tobychui/DIY-60W-PD-Powerbank/Photo/273100965_10218137502903919_1505471354527480093_n.jpg

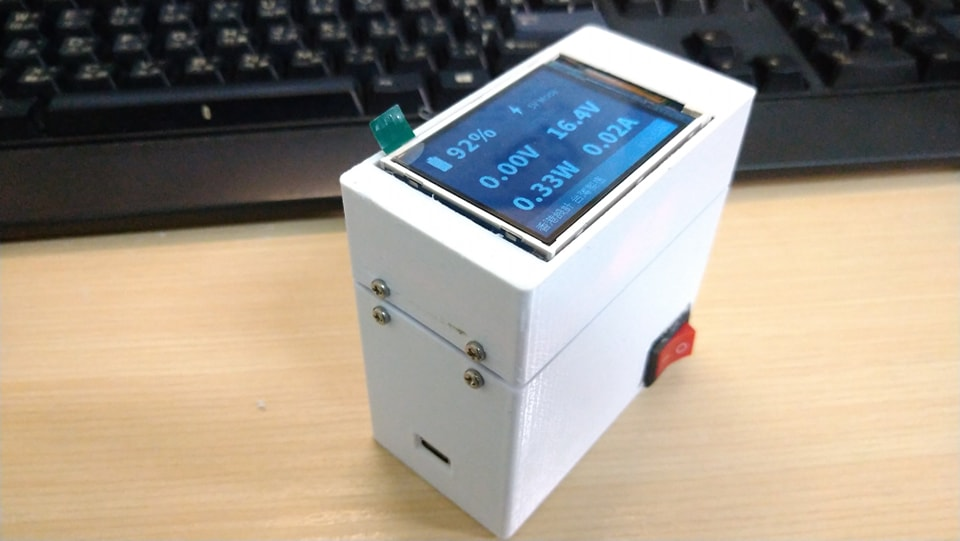
Photo/273100965_10218137502903919_1505471354527480093_n.jpg
