tobychui/DIY-60W-PD-Powerbank/Photo/DSC_0626.JPG

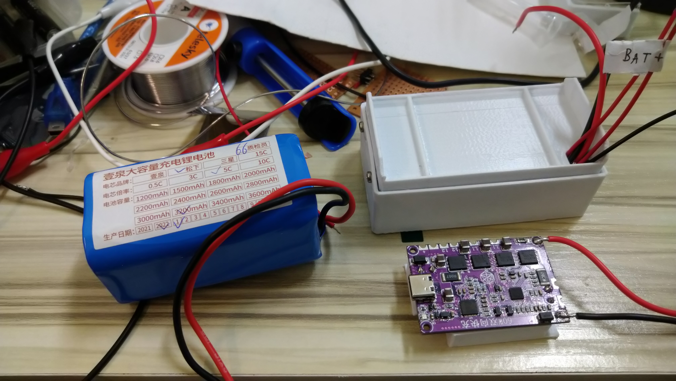
Photo/DSC_0626.JPG
