tobychui/DIY-60W-PD-Powerbank/Photo/DSC_0627.JPG

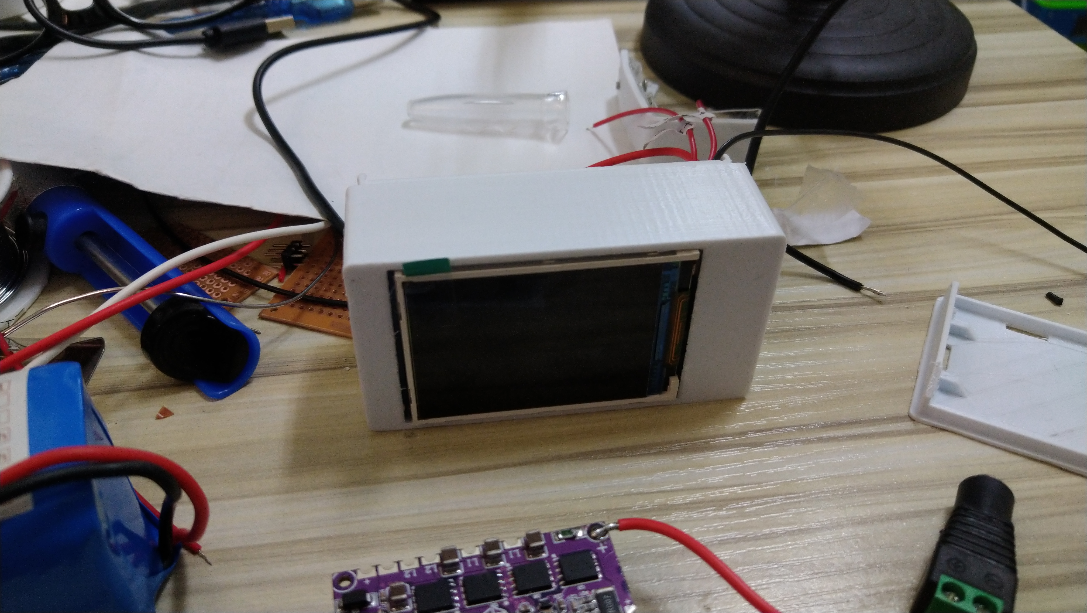
Photo/DSC_0627.JPG
