tobychui/DIY-60W-PD-Powerbank/Photo/DSC_0629.JPG

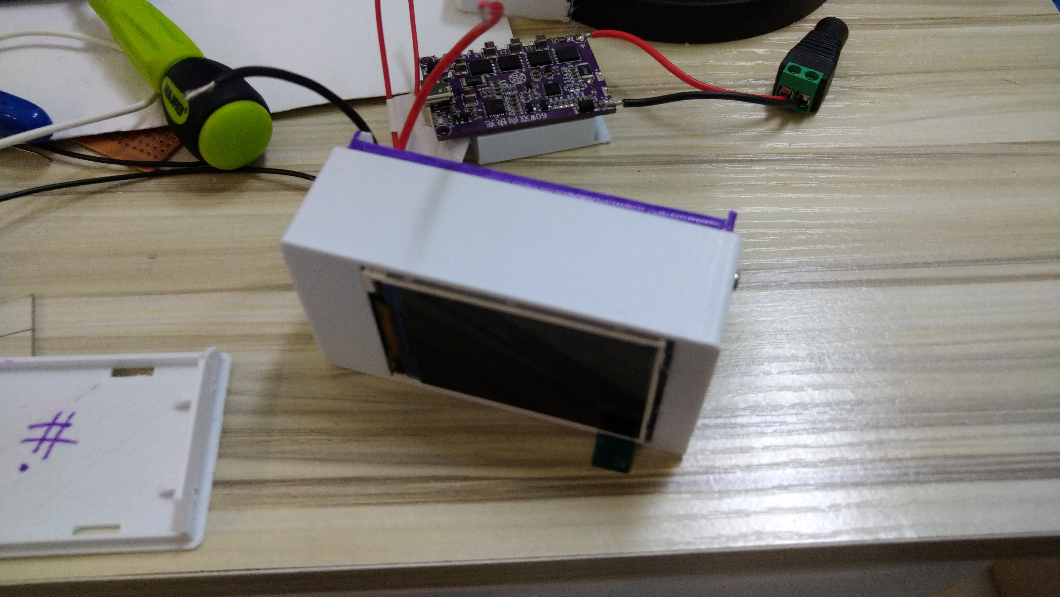
Photo/DSC_0629.JPG
