tobychui/DIY-60W-PD-Powerbank/Photo/DSC_0630.JPG

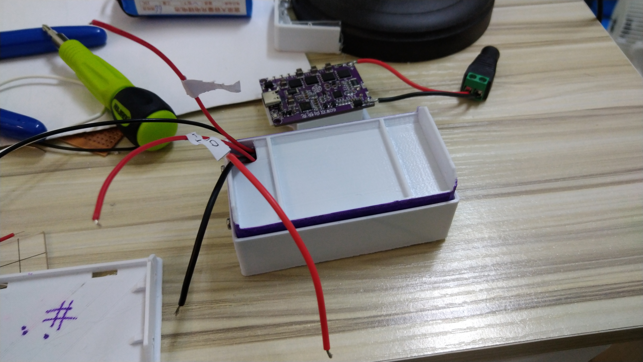
Photo/DSC_0630.JPG
