tobychui/DIY-60W-PD-Powerbank/Photo/DSC_0631.JPG

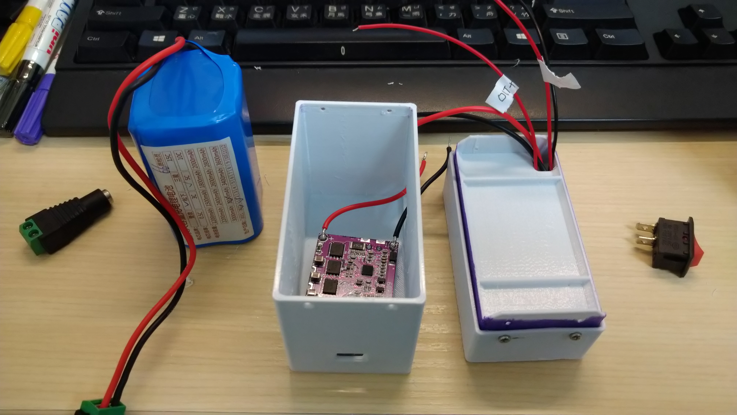
Photo/DSC_0631.JPG
