tobychui/DIY-60W-PD-Powerbank/Photo/DSC_0632.JPG

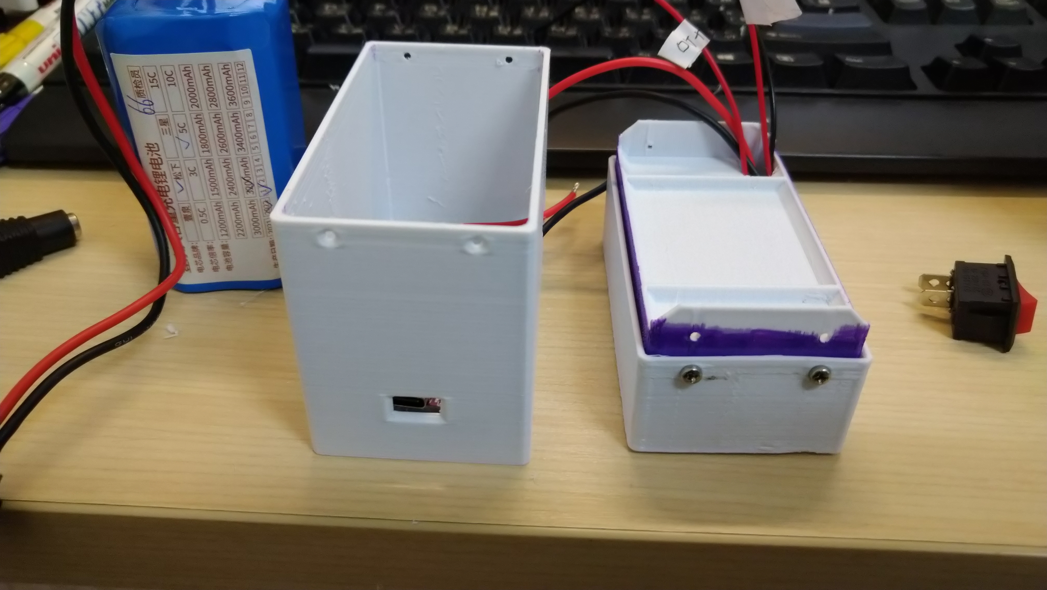
Photo/DSC_0632.JPG
