tobychui/DIY-60W-PD-Powerbank/Photo/IMG_20220121_200404.jpg

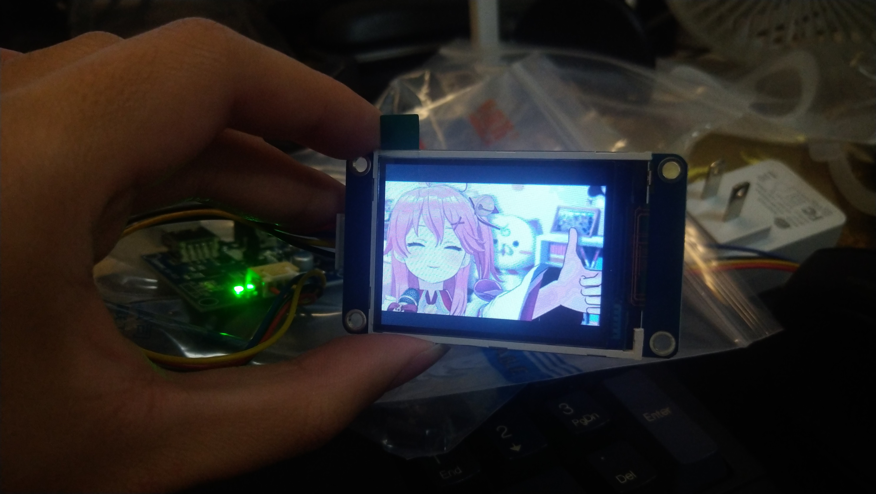
Photo/IMG_20220121_200404.jpg
