tobychui/DIY-60W-PD-Powerbank/Photo/IMG_20220121_230231.jpg

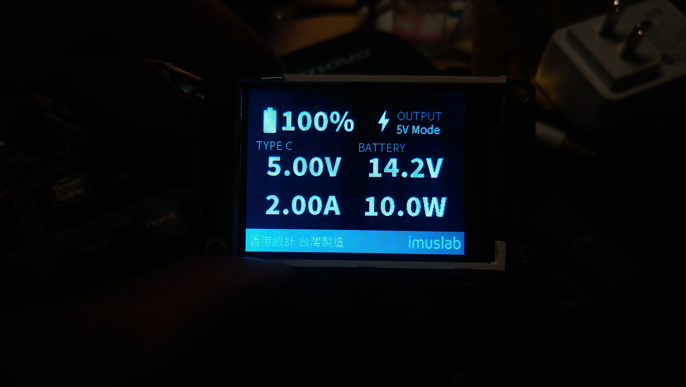
Photo/IMG_20220121_230231.jpg
