tobychui/DIY-60W-PD-Powerbank/Photo/IMG_20220121_230241.jpg

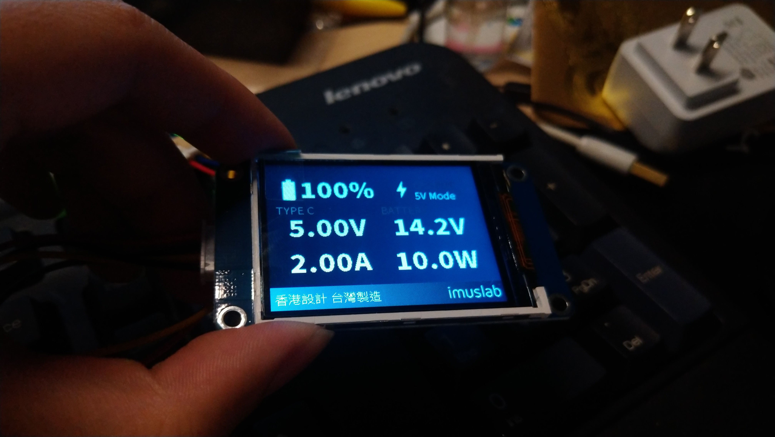
Photo/IMG_20220121_230241.jpg
