tobychui/DIY-60W-PD-Powerbank/Photo/IMG_20220125_193211.jpg

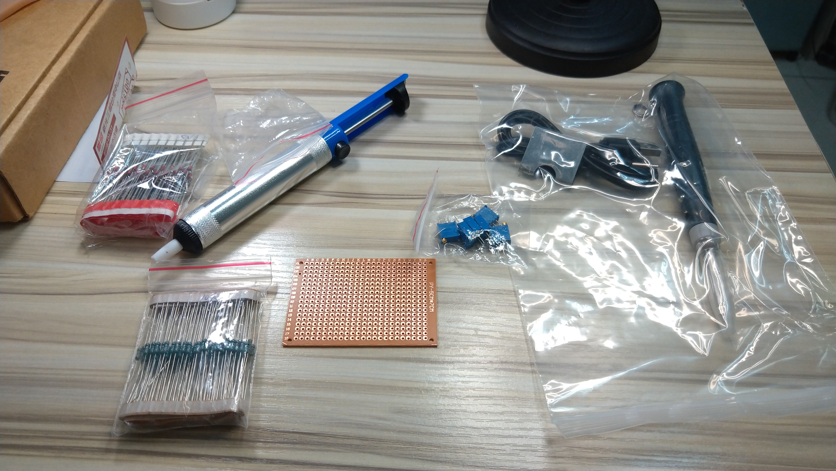
Photo/IMG_20220125_193211.jpg
