tobychui/DIY-60W-PD-Powerbank/Photo/IMG_20220125_210157.jpg

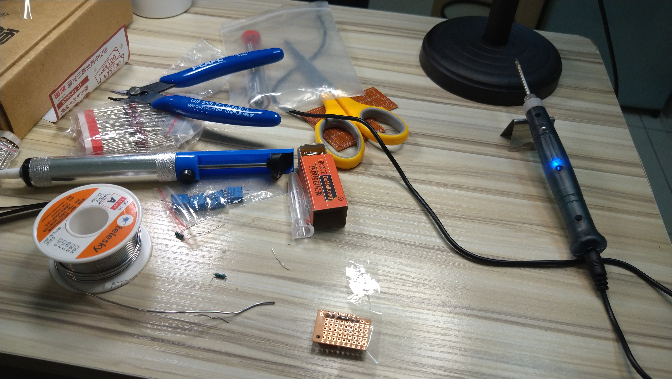
Photo/IMG_20220125_210157.jpg
