tobychui/DIY-60W-PD-Powerbank/Photo/IMG_20220125_210558.jpg

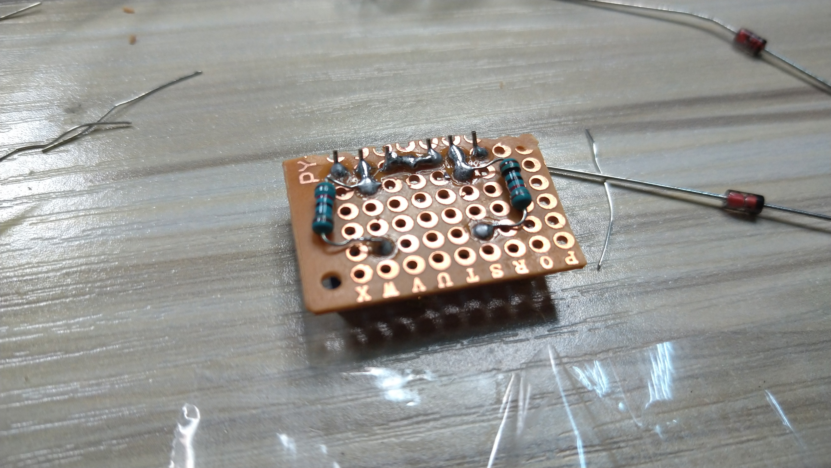
Photo/IMG_20220125_210558.jpg
