tobychui/DIY-60W-PD-Powerbank/Photo/IMG_20220125_210615.jpg

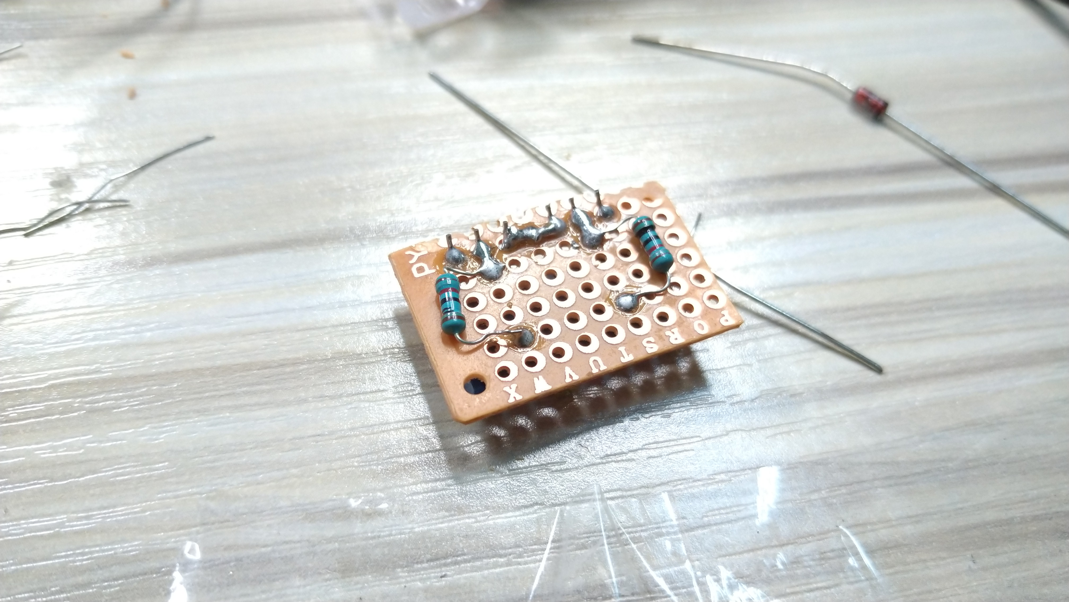
Photo/IMG_20220125_210615.jpg
