tobychui/DIY-60W-PD-Powerbank/Photo/IMG_20220125_213329.jpg

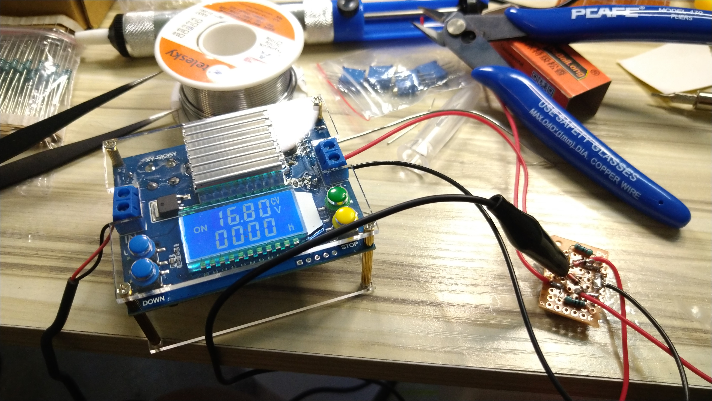
Photo/IMG_20220125_213329.jpg
