tobychui/DIY-60W-PD-Powerbank/Photo/IMG_20220125_214237.jpg

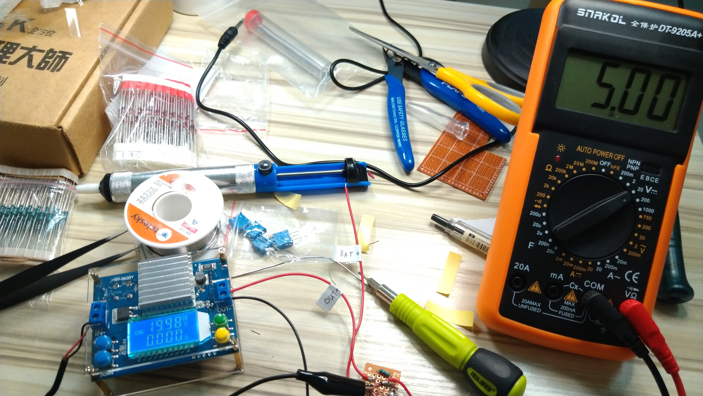
Photo/IMG_20220125_214237.jpg
