tobychui/DIY-60W-PD-Powerbank/Photo/IMG_20220126_150131.jpg

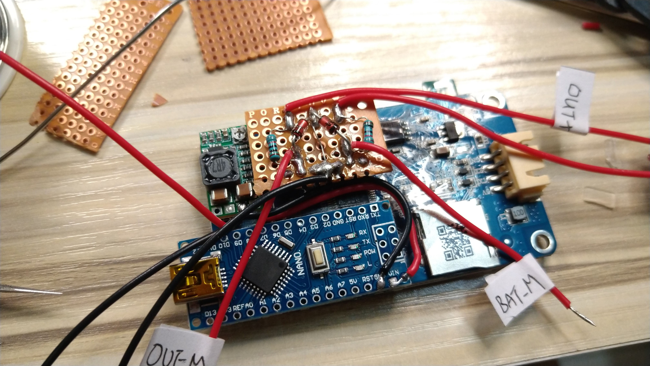
Photo/IMG_20220126_150131.jpg
