tobychui/DIY-60W-PD-Powerbank/Photo/IMG_20220126_150137.jpg

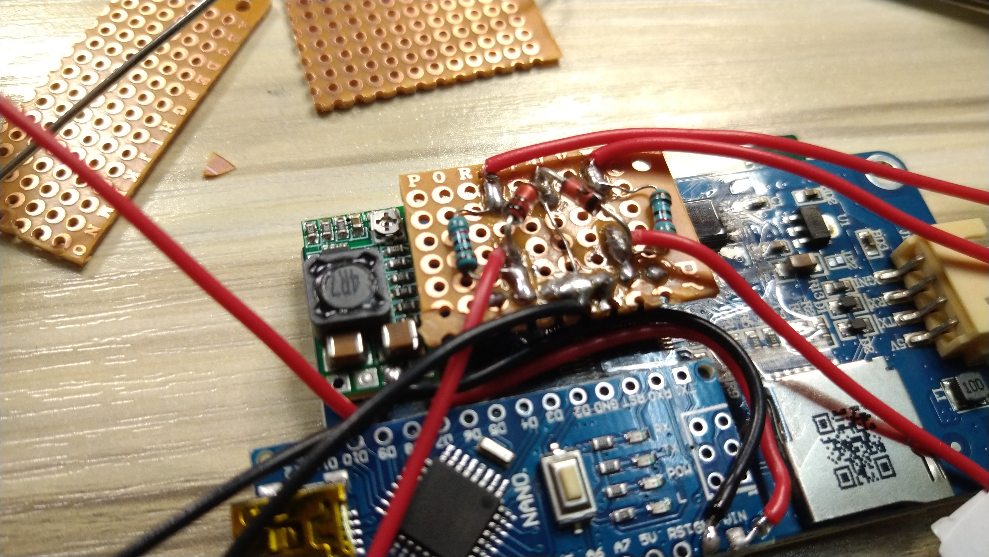
Photo/IMG_20220126_150137.jpg
