tobychui/DIY-60W-PD-Powerbank/Photo/IMG_20220126_181836.jpg

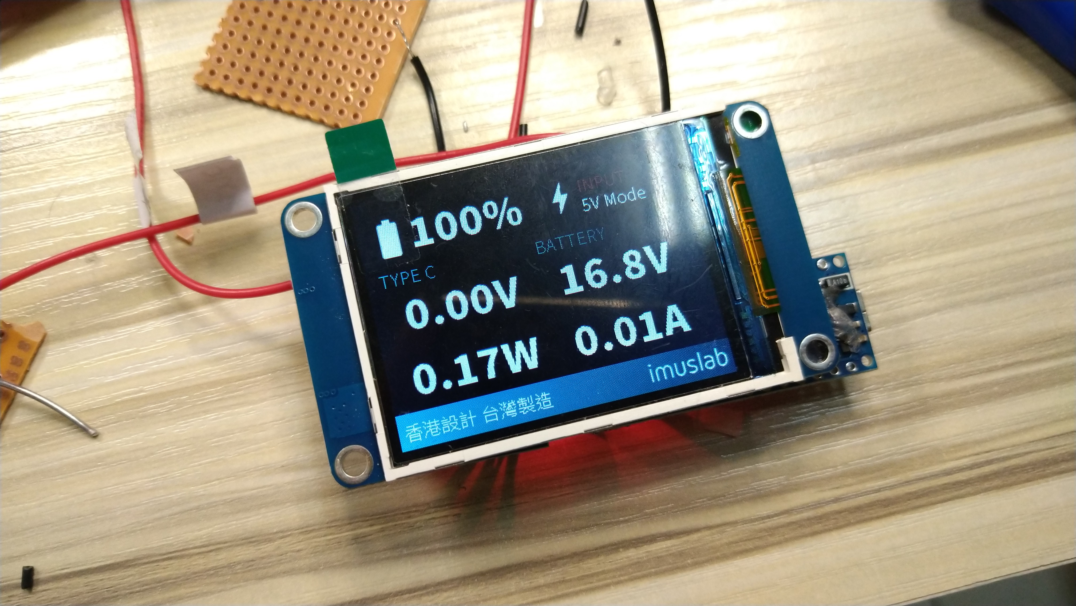
Photo/IMG_20220126_181836.jpg
