tobychui/DIY-60W-PD-Powerbank/Photo/IMG_20220126_181847.jpg

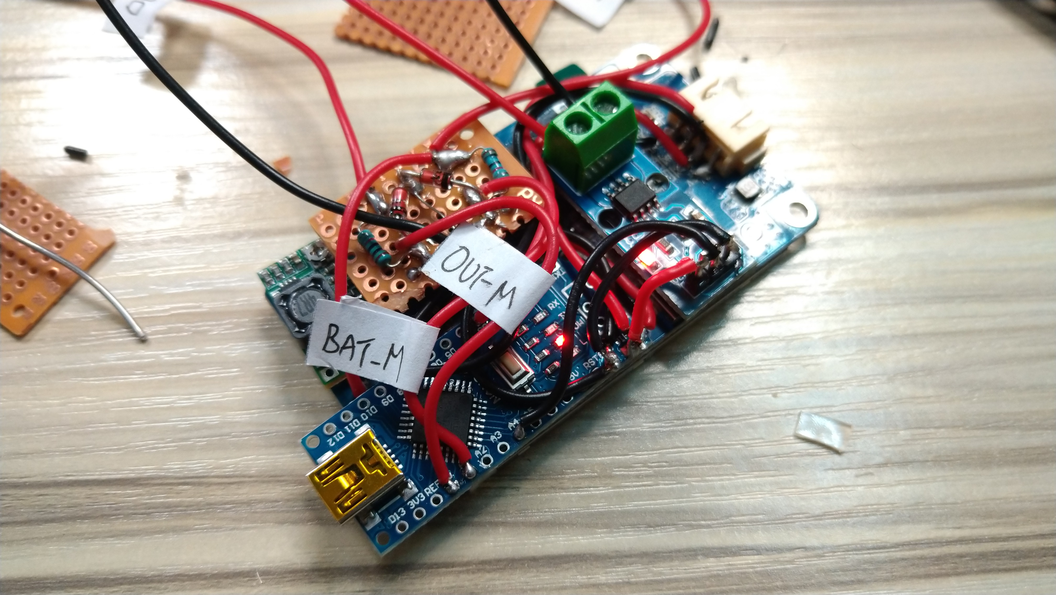
Photo/IMG_20220126_181847.jpg
