tobychui/DIY-60W-PD-Powerbank/Photo/IMG_20220126_205837.jpg

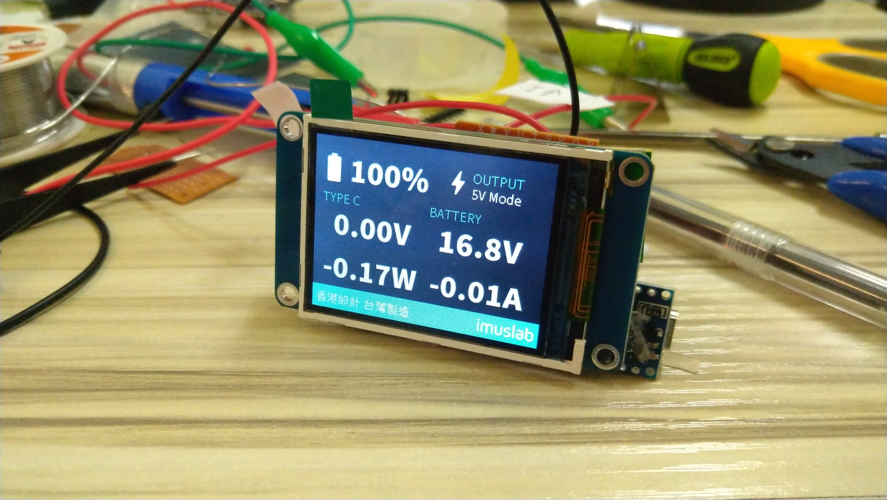
Photo/IMG_20220126_205837.jpg
