tobychui/DIY-60W-PD-Powerbank/Photo/IMG_20220130_222910.jpg

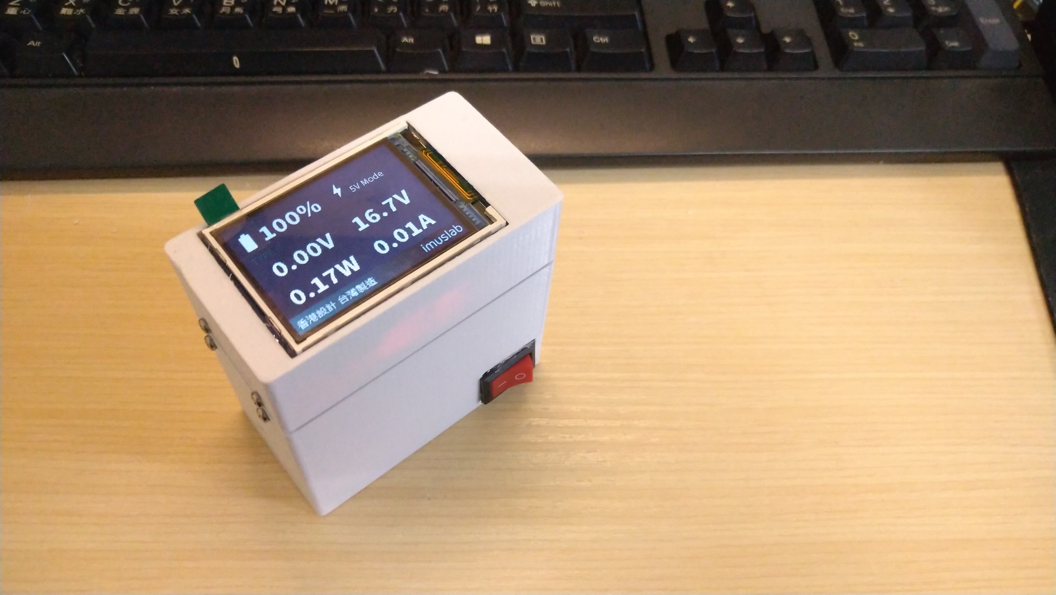
Photo/IMG_20220130_222910.jpg
