tobychui/DIY-60W-PD-Powerbank/Photo/IMG_20220130_222922.jpg

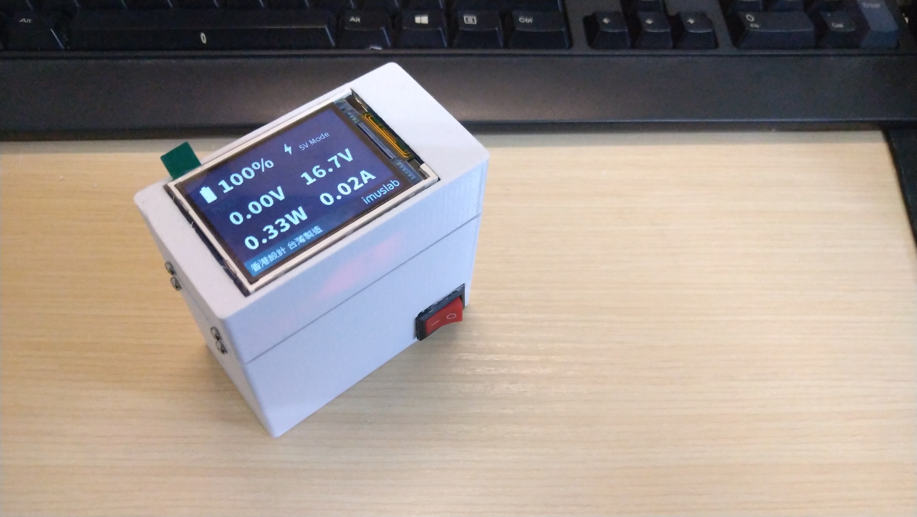
Photo/IMG_20220130_222922.jpg
