tobychui/DIY-60W-PD-Powerbank/Rendering/untitled.1.png

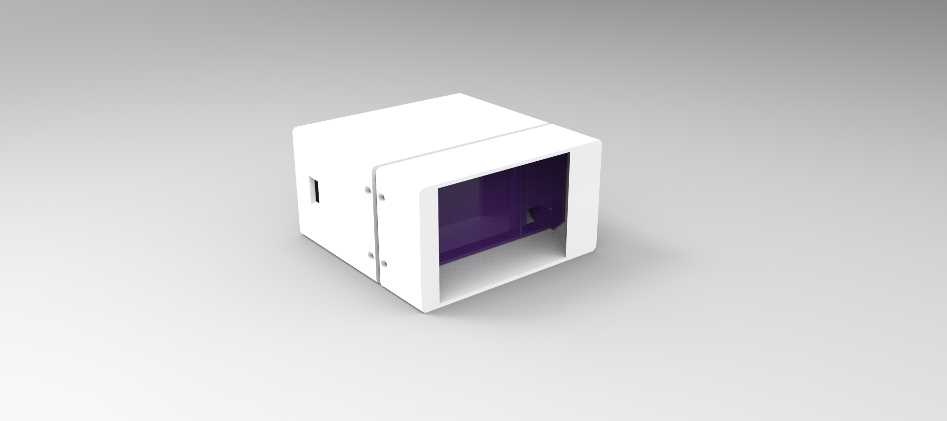
Rendering/untitled.1.png
