tobychui/DIY-60W-PD-Powerbank/Rendering/untitled.2.png

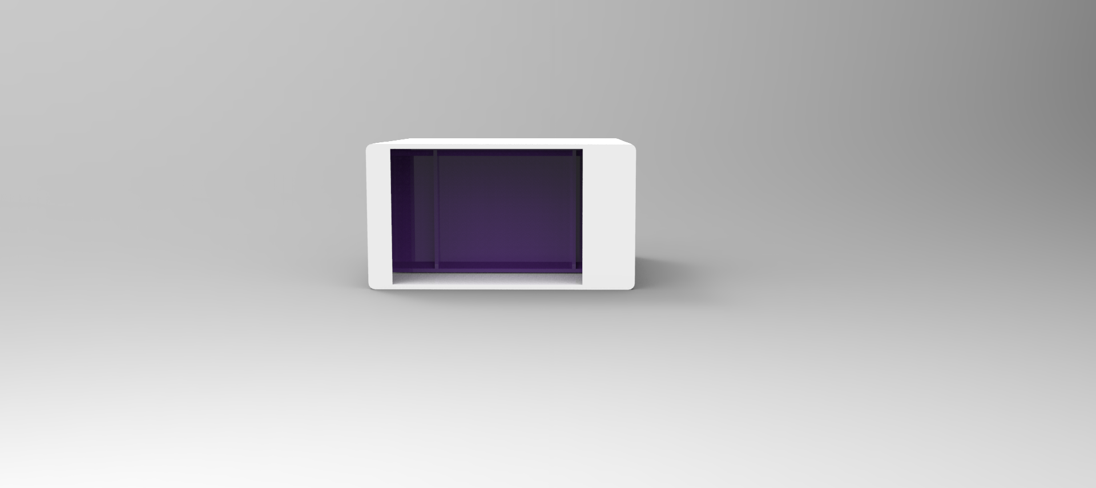
Rendering/untitled.2.png
