tobychui/DIY-60W-PD-Powerbank/Rendering/untitled.3.png

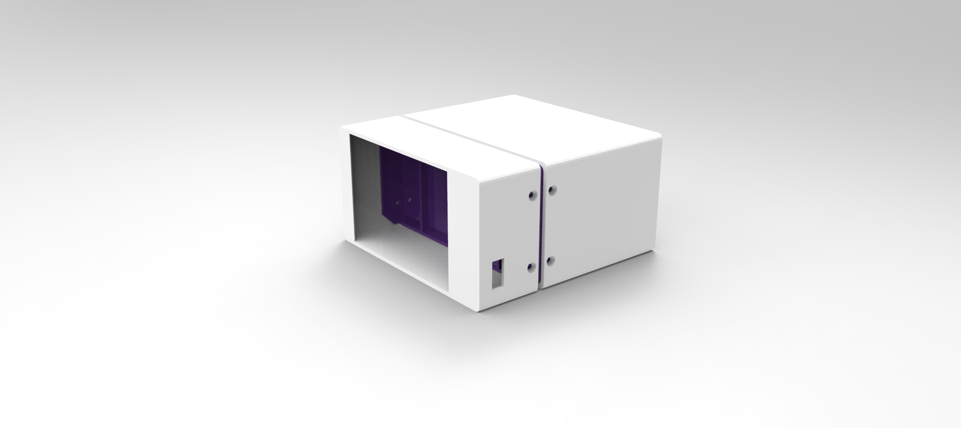
Rendering/untitled.3.png
