tobychui/DIY-60W-PD-Powerbank/Rendering/untitled.4.png

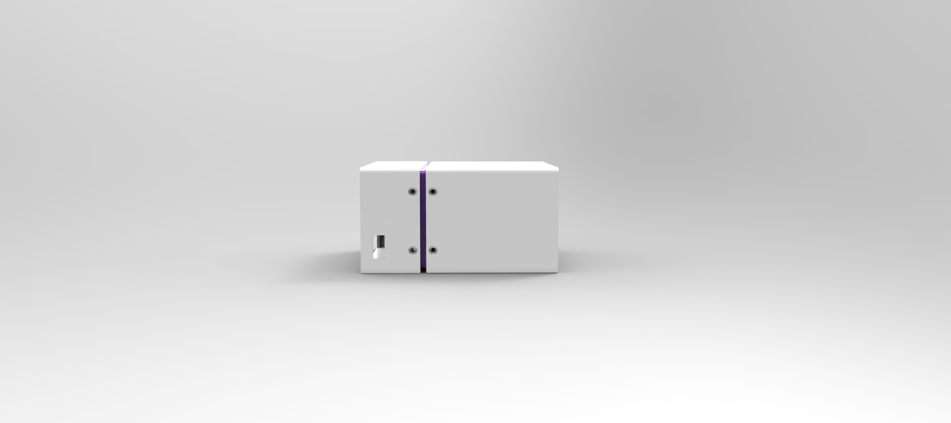
Rendering/untitled.4.png
