tobychui/DIY-60W-PD-Powerbank/Rendering/untitled.5.png

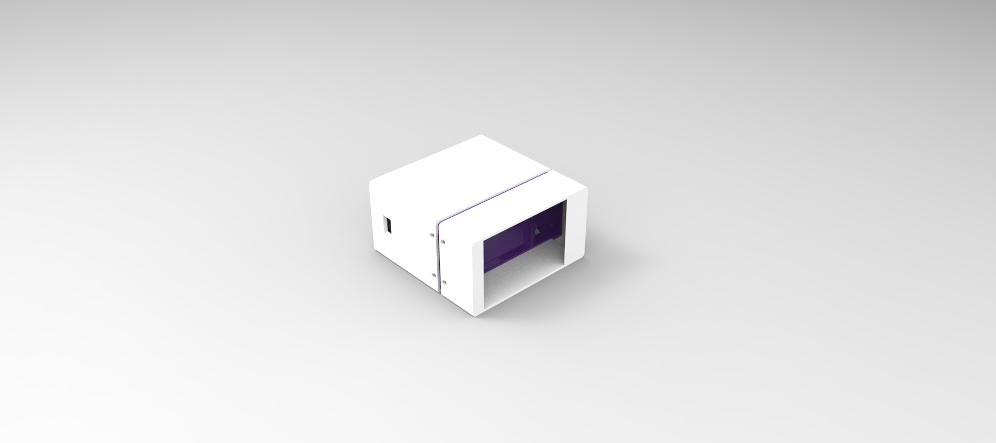
Rendering/untitled.5.png
