tobychui/DIY-60W-PD-Powerbank/Rendering/untitled.6.png

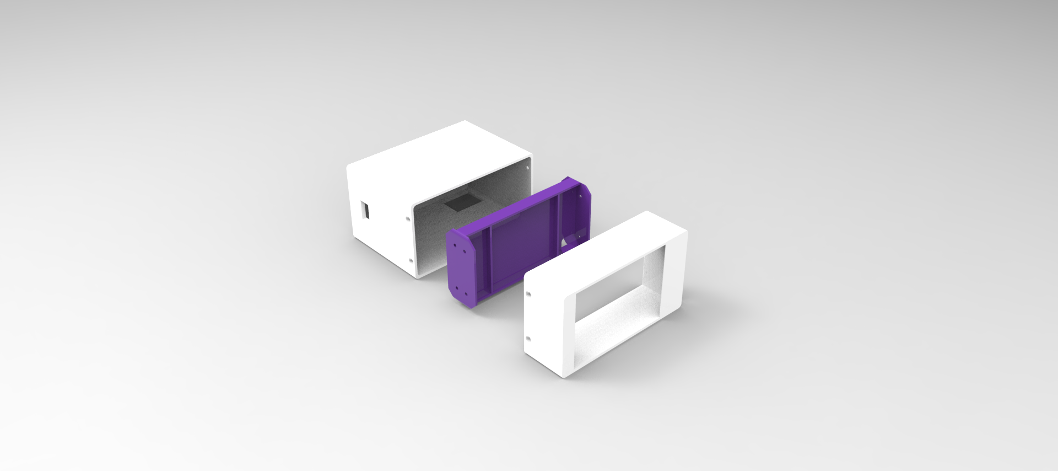
Rendering/untitled.6.png
