tobychui/DIY-60W-PD-Powerbank/Rendering/untitled.7.png

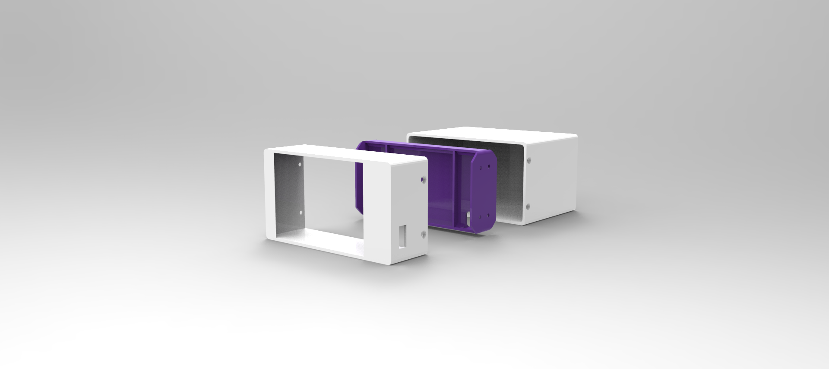
Rendering/untitled.7.png
