tobychui/DIY-60W-PD-Powerbank/UART HMI Code/loading.png

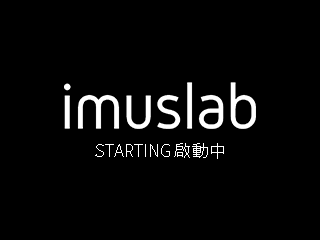
UART HMI Code/loading.png
