tobychui/DIY-60W-PD-Powerbank/UART HMI Code/main.png

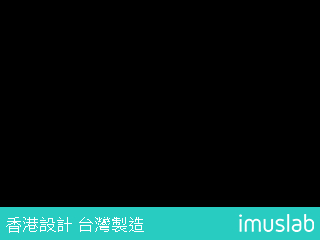
UART HMI Code/main.png
